calcite/Sonochan-mkII/DOC/drawings/internal_external_schema.png

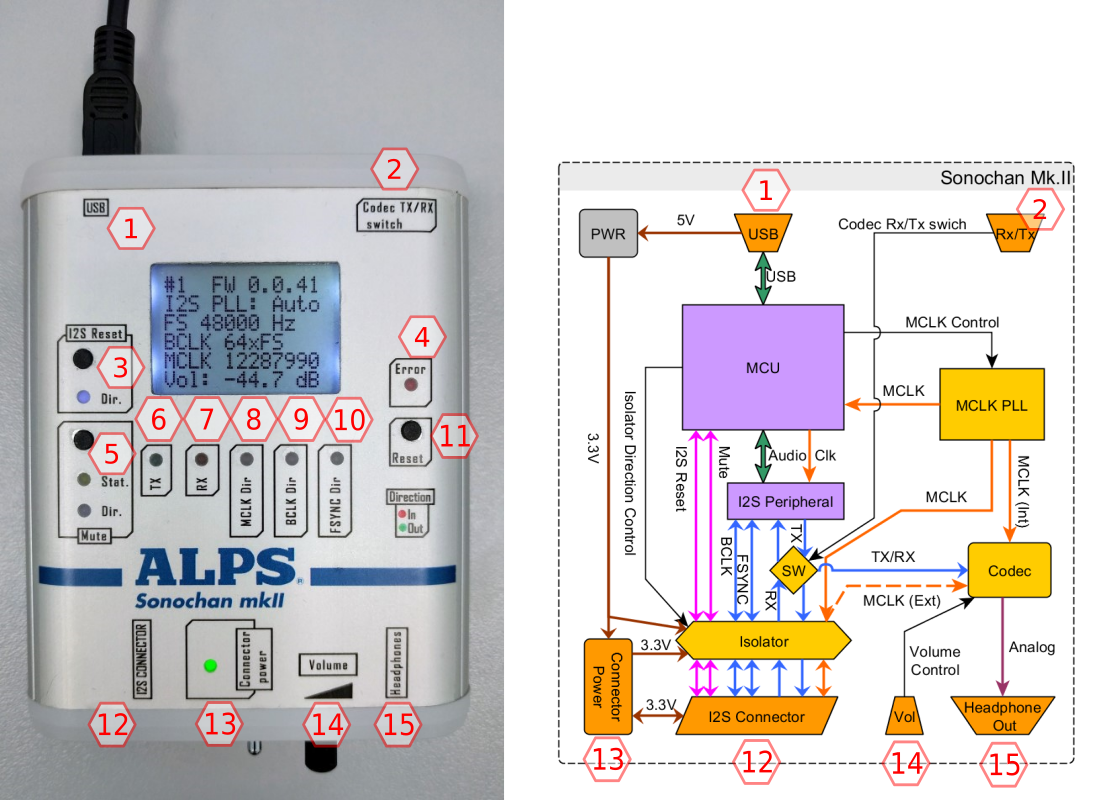
DOC/drawings/internal_external_schema.png
