calcite/Sonochan-mkII/DOC/drawings/isolation_schema.png

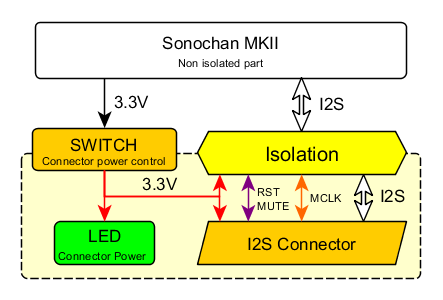
DOC/drawings/isolation_schema.png
