calcite/Sonochan-mkII/DOC/drawings/lcd_schema.png

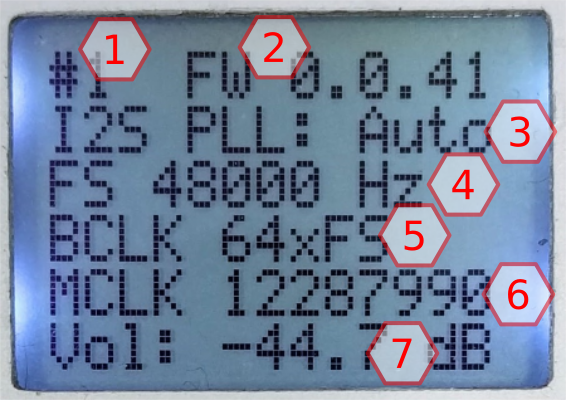
DOC/drawings/lcd_schema.png
