calcite/Sonochan-mkII/DOC/drawings/sonochan_internal_workings.png

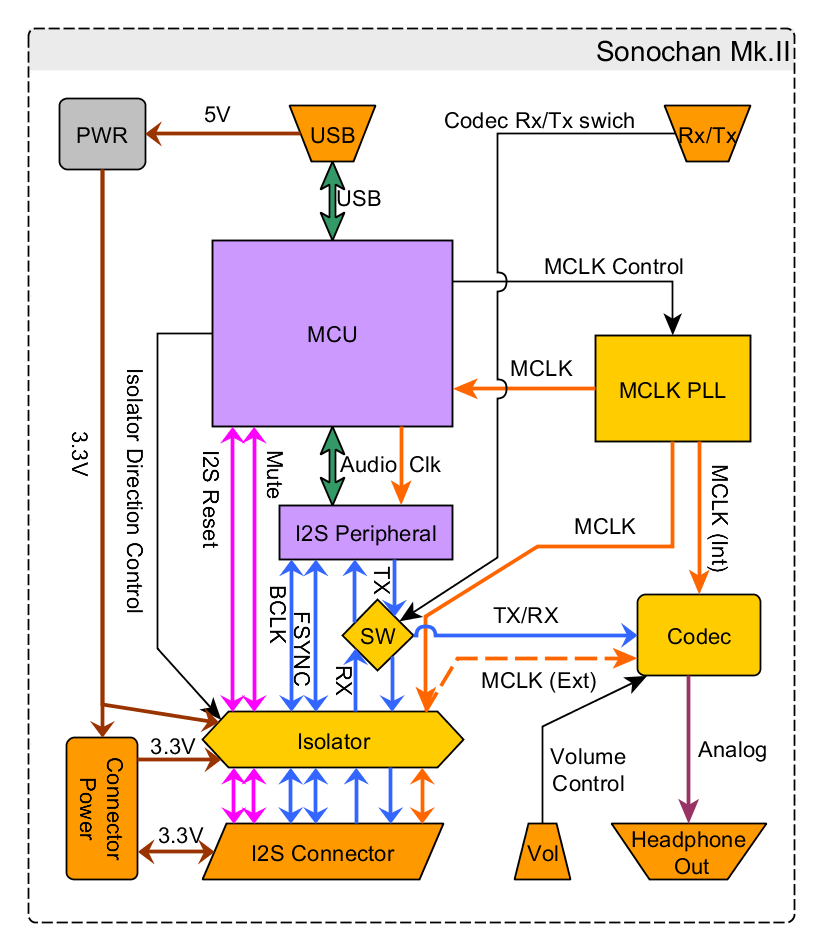
DOC/drawings/sonochan_internal_workings.png
