calcite/Sonochan-mkII/DOC/photo/snchn_mkII_complete.JPG

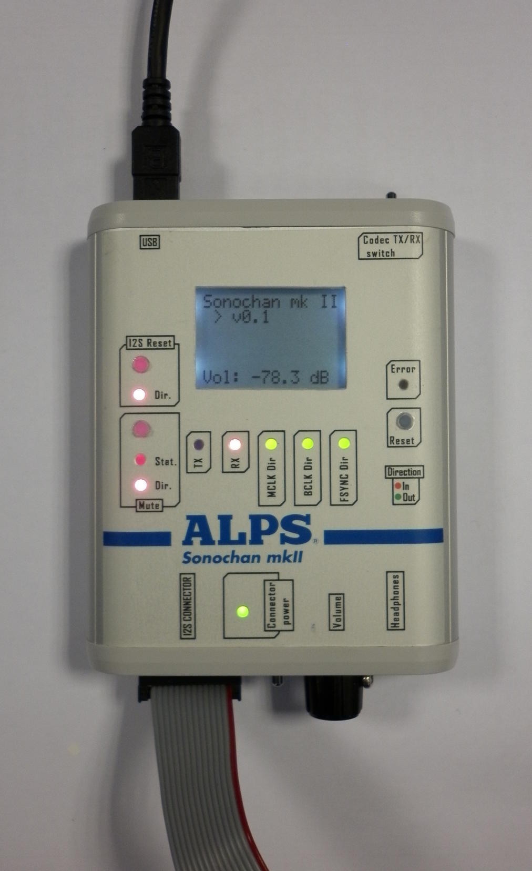
DOC/photo/snchn_mkII_complete.JPG
