calcite/Sonochan-mkII/DOC/photo/snchn_mkII_complete_enhanced.png

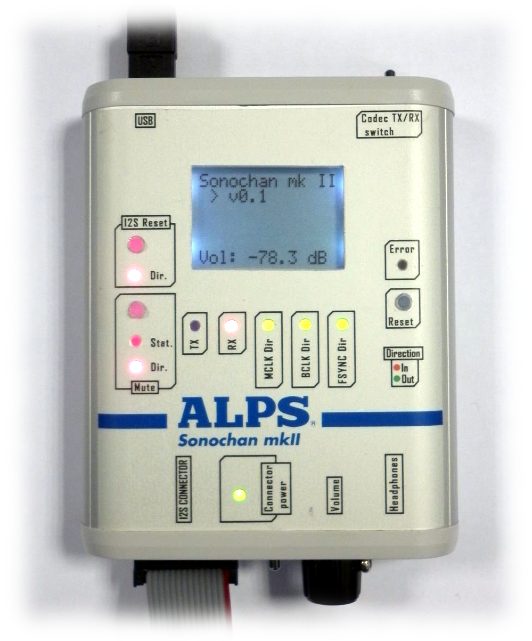
DOC/photo/snchn_mkII_complete_enhanced.png
