calcite/Sonochan-mkII/DOC/photo/snchn_mkII_complete_in_case.jpg

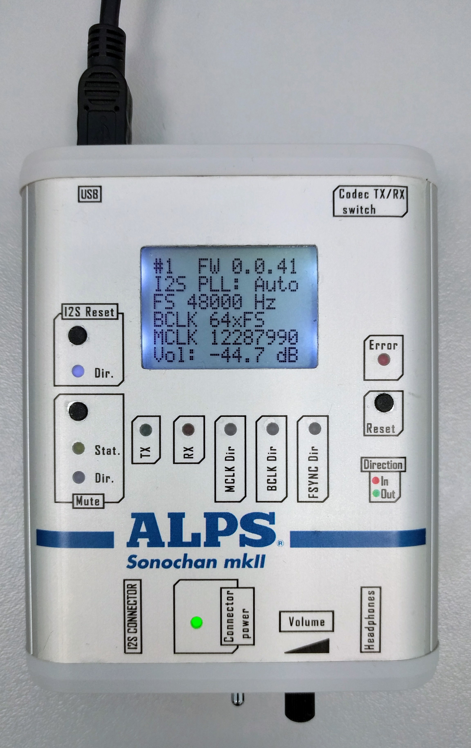
DOC/photo/snchn_mkII_complete_in_case.jpg
