calcite/Sonochan-mkII/DOC/photo/snchn_mkII_LCD_small.png

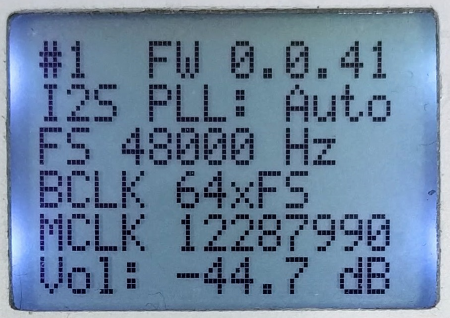
DOC/photo/snchn_mkII_LCD_small.png
