calcite/Sonochan-mkII/DOC/photo/snchn_mkII_sdr_wgt_prototype_top.JPG

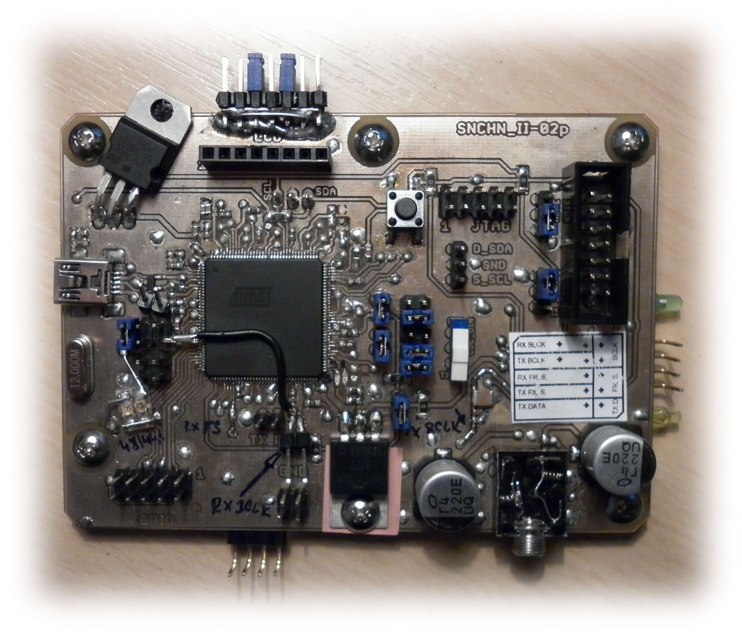
DOC/photo/snchn_mkII_sdr_wgt_prototype_top.JPG
