calcite/Sonochan-mkII/DOC/photo/snchn_mkII_top_in_case.JPG

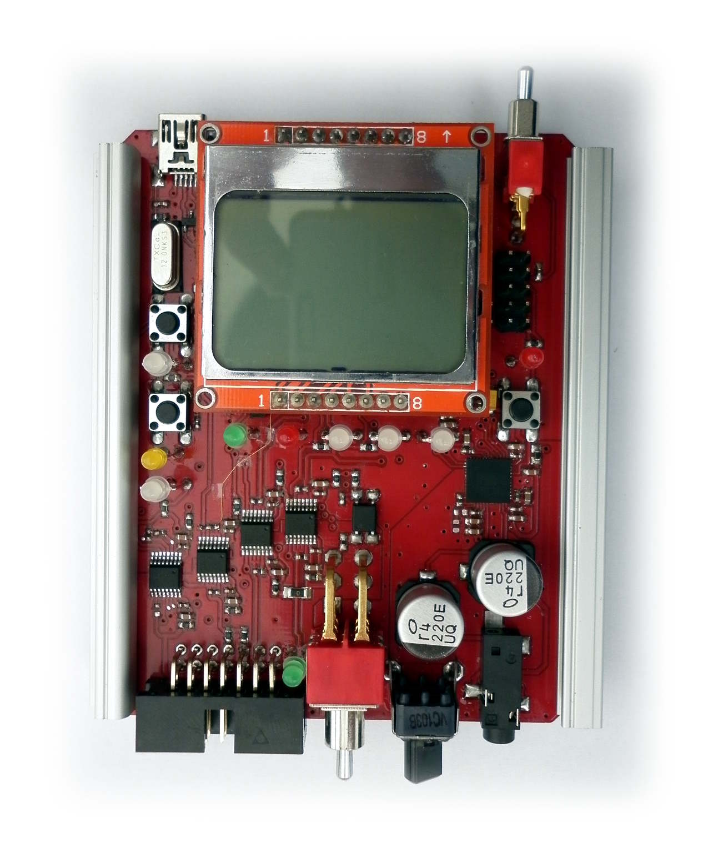
DOC/photo/snchn_mkII_top_in_case.JPG
