calcite/Sonochan-mkII/DOC/thesis/thesis_doc_files/bridge_get_metadata.gif

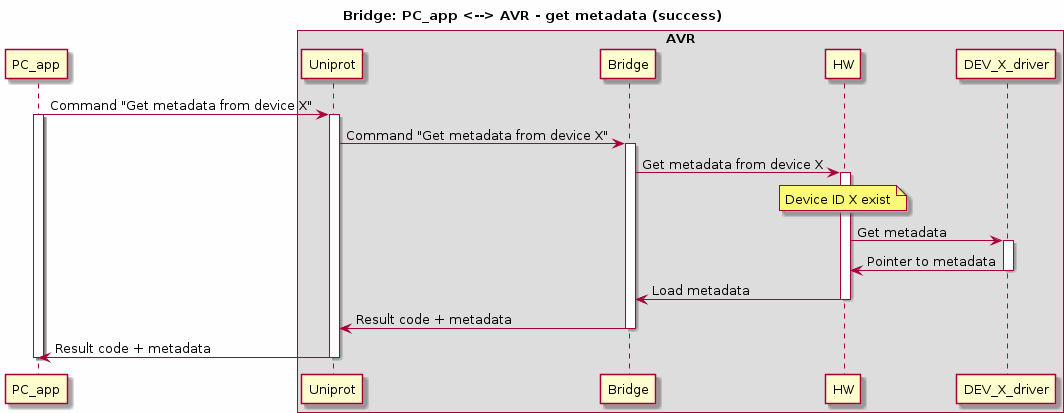
DOC/thesis/thesis_doc_files/bridge_get_metadata.gif
