calcite/Sonochan-mkII/DOC/thesis/thesis_doc_files/bridge_get_num_of_dev.gif

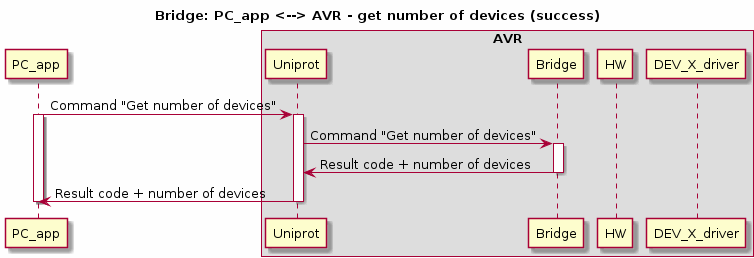
DOC/thesis/thesis_doc_files/bridge_get_num_of_dev.gif
