calcite/Sonochan-mkII/DOC/thesis/thesis_doc_files/bridge_get_setting_did_invalid.gif

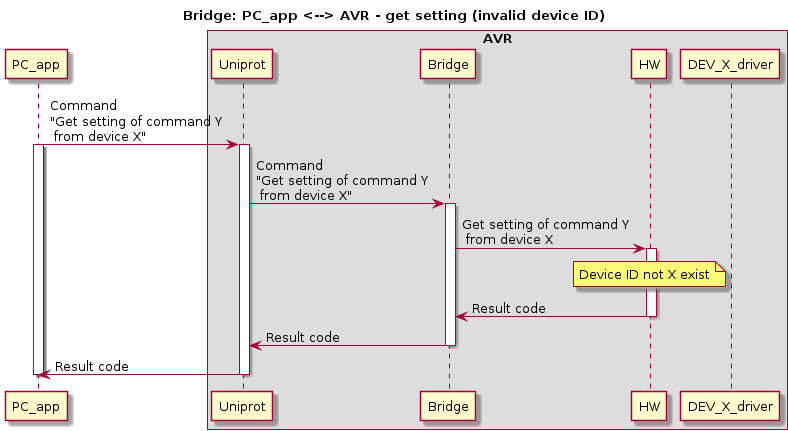
DOC/thesis/thesis_doc_files/bridge_get_setting_did_invalid.gif
