calcite/Sonochan-mkII/DOC/thesis/thesis_doc_files/bridge_set_setting_all_OK.gif

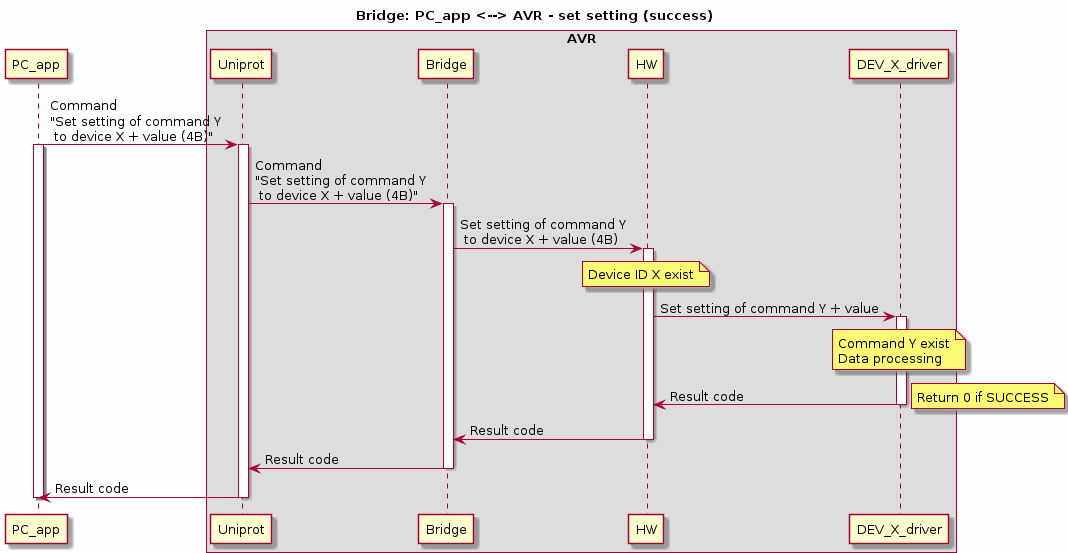
DOC/thesis/thesis_doc_files/bridge_set_setting_all_OK.gif
