calcite/Sonochan-mkII/DOC/thesis/thesis_doc_files/host_set_sampling_freq.gif

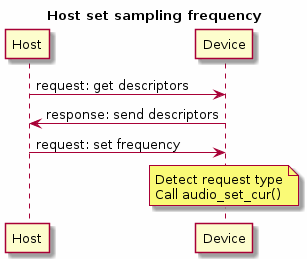
DOC/thesis/thesis_doc_files/host_set_sampling_freq.gif
