calcite/Sonochan-mkII/DOC/thesis/thesis_doc_files/uniprot_ACK.gif

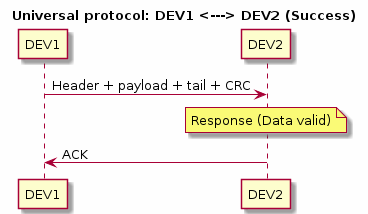
DOC/thesis/thesis_doc_files/uniprot_ACK.gif
