calcite/Sonochan-mkII/DOC/thesis/thesis_doc_files/uniprot_BUFF_OVRFLW.gif

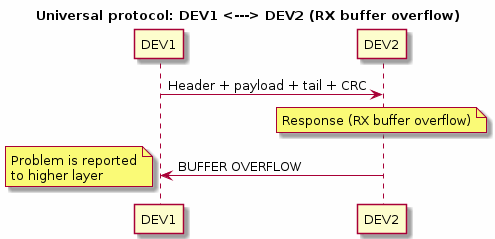
DOC/thesis/thesis_doc_files/uniprot_BUFF_OVRFLW.gif
