calcite/Sonochan-mkII/DOC/thesis/thesis_doc_files/uniprot_NACK.gif

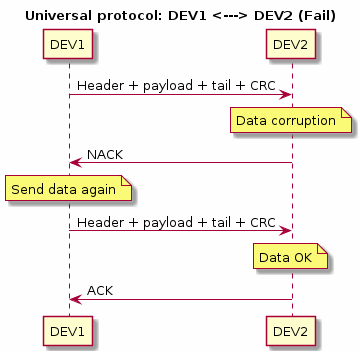
DOC/thesis/thesis_doc_files/uniprot_NACK.gif
