calcite/Sonochan-mkII/PRODUCTION_DATA/stickers/i2s_connector_description.png

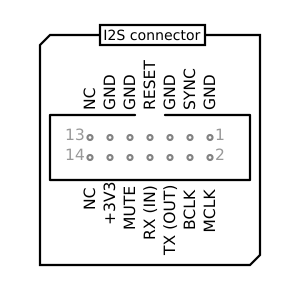
PRODUCTION_DATA/stickers/i2s_connector_description.png
