calcite/Sonochan-mkII/PRODUCTION_DATA/stickers/SNCHN_II-02p_Extra_sticker.pdf

123

11

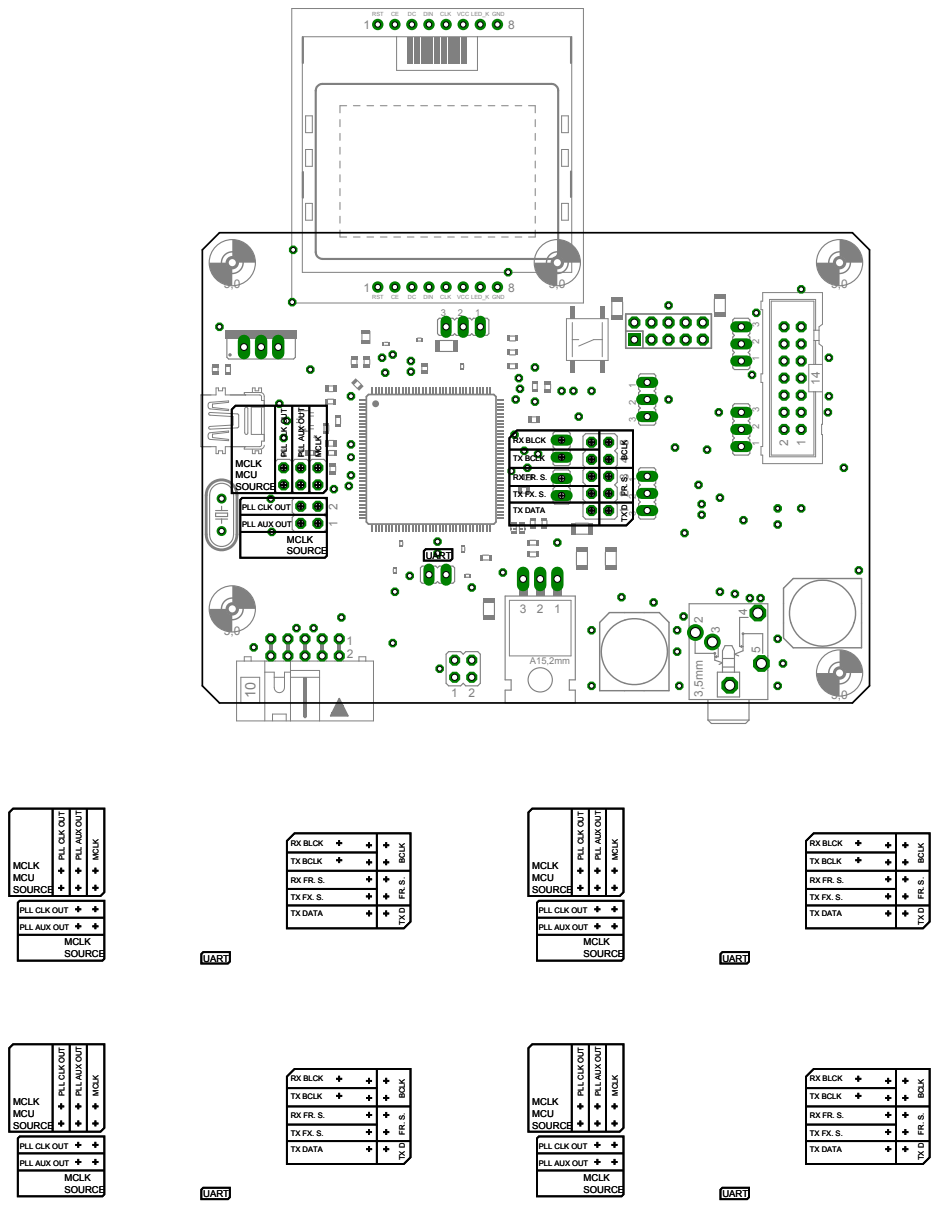
[picture p71: page 1]
RST; DC DIN CLK VCC LED_K GND; MCLK SOURCE; MCLK MCU SOURCE; MCLK; UART; BCLK; RX BLCK; TX BCLK; TX DATA

PLL CLK OUT

PLL AUX OUT
