calcite/Sonochan-mkII/HW/Eagle_exports/SNCHN_II-02p_top_mirrored.pdf

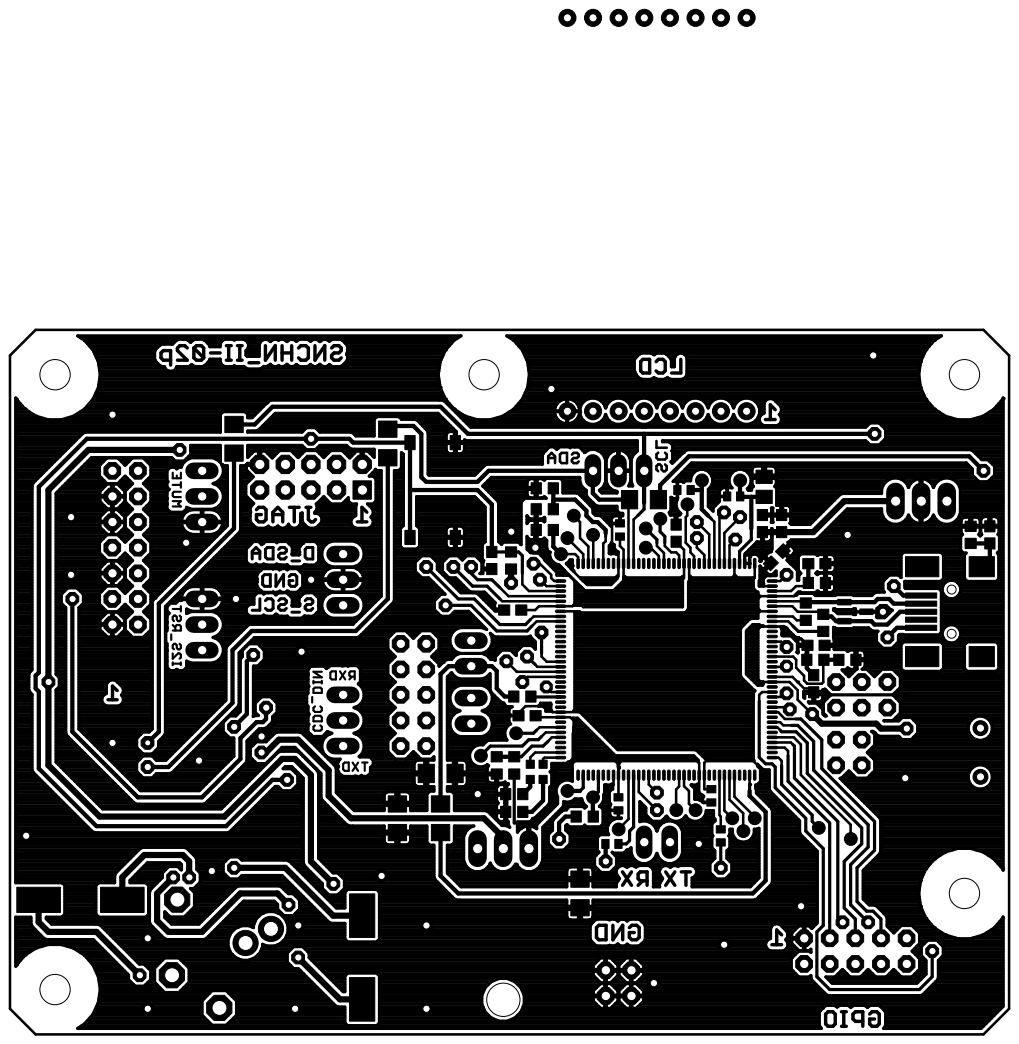
[picture p81: page 1]
