calcite/Sonochan-mkII/HW/Eagle_exports/SNCHN_II-03-brd_15.pdf

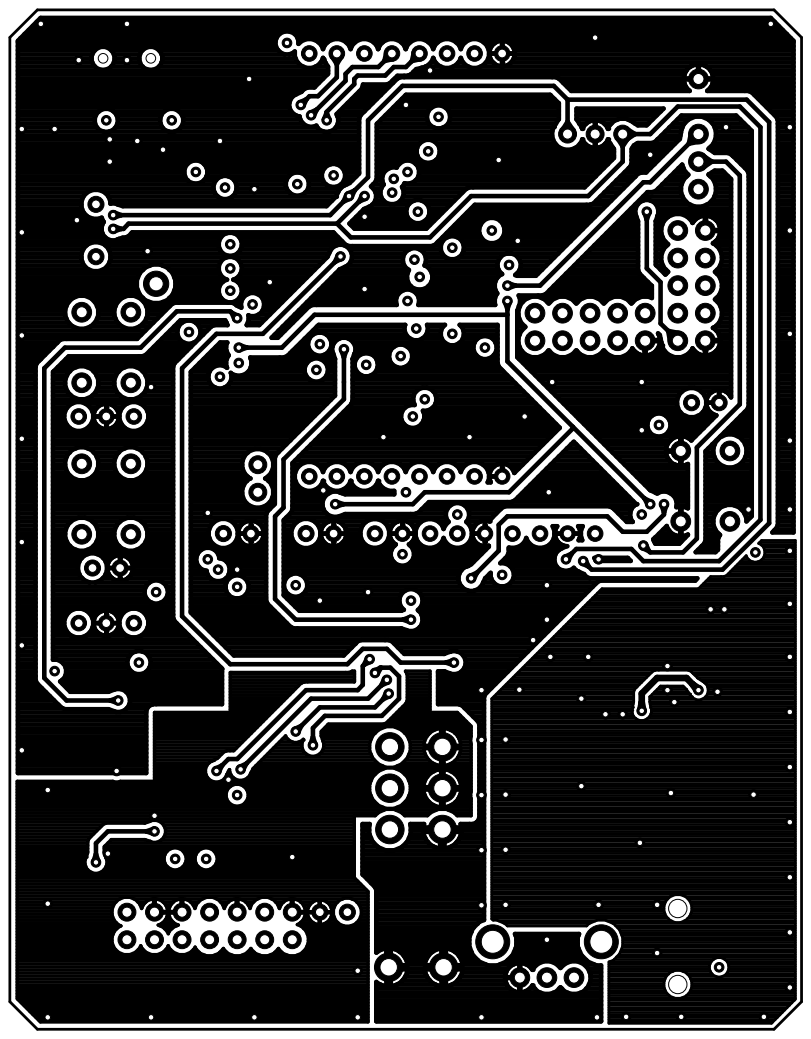
[picture p82: page 1]
