calcite/Sonochan-mkII/HW/Eagle_exports/SNCHN_II-03-brd_2.pdf

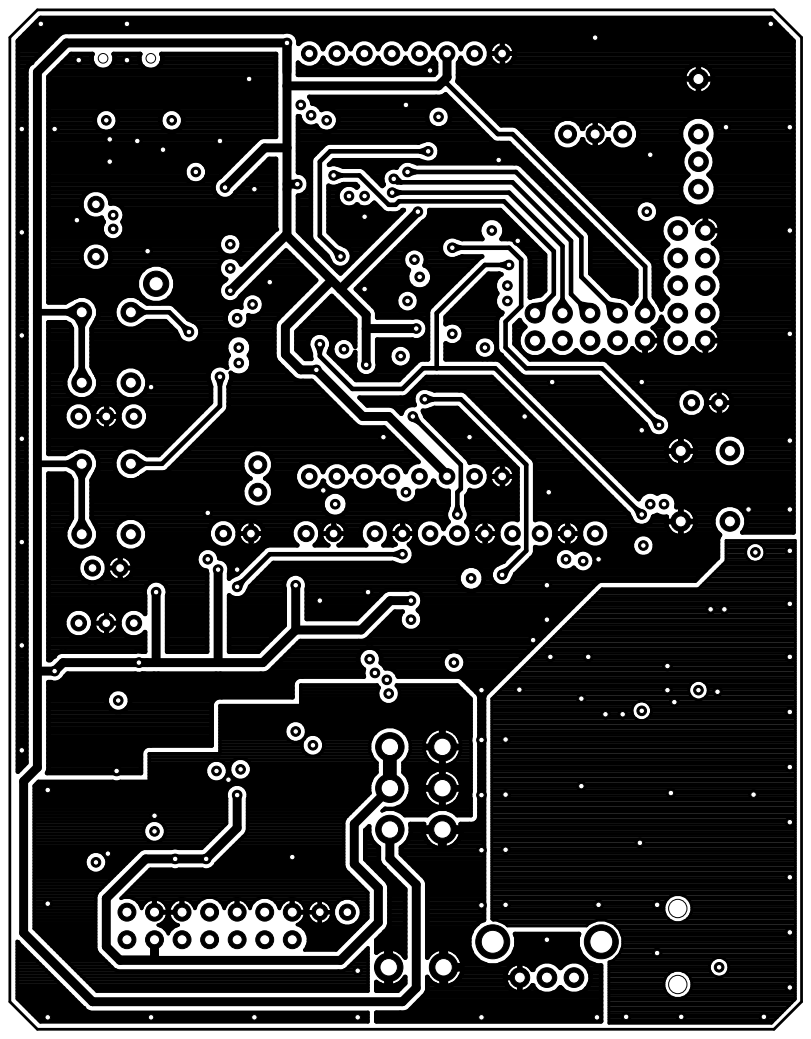
[picture p83: page 1]
