calcite/Sonochan-mkII/HW/Eagle_exports/SNCHN_II-03-brd_bottom.pdf

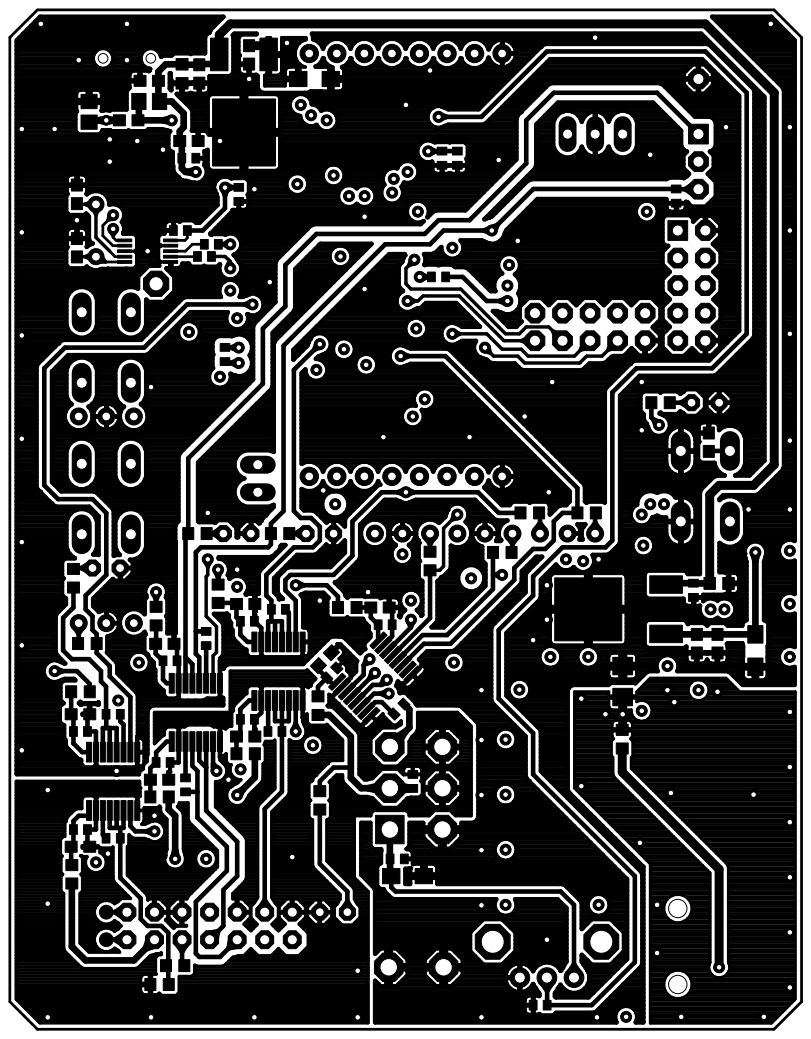
[picture p84: page 1]
