calcite/Sonochan-mkII/HW/Eagle_exports/SNCHN_II-03-brd_top.pdf

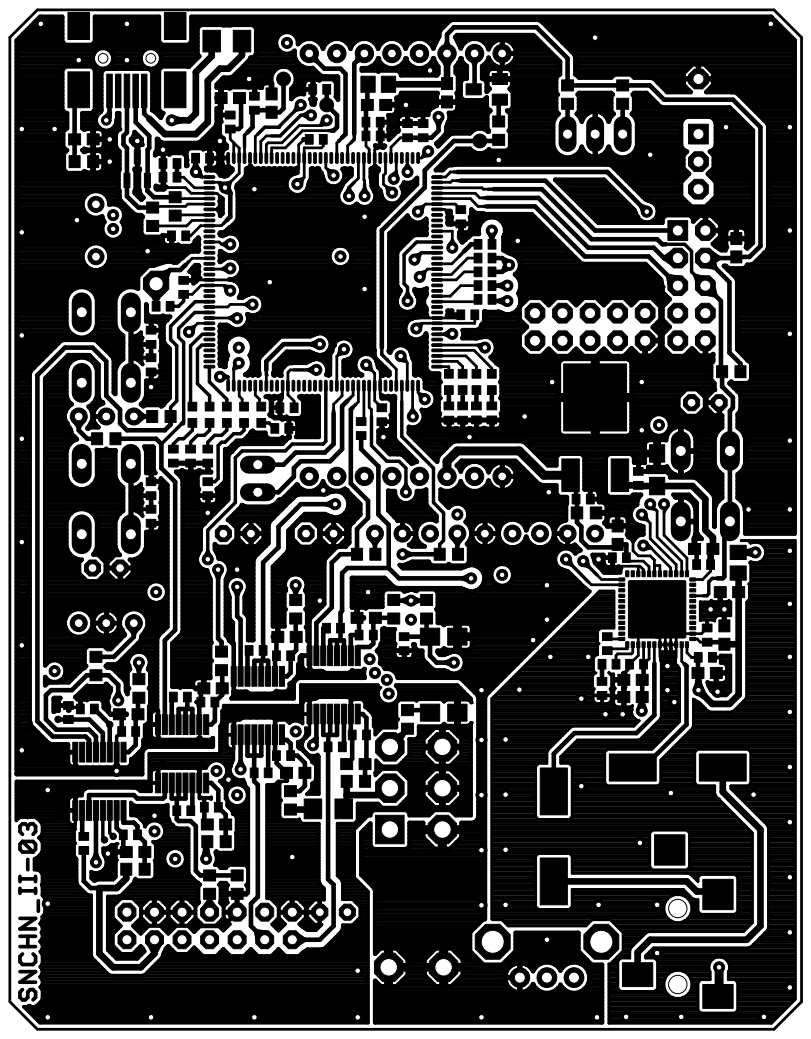
[picture p85: page 1]
