calcite/Sonochan-mkII/HW/Eagle_exports/SNCHN_II-03A-brd_15.pdf

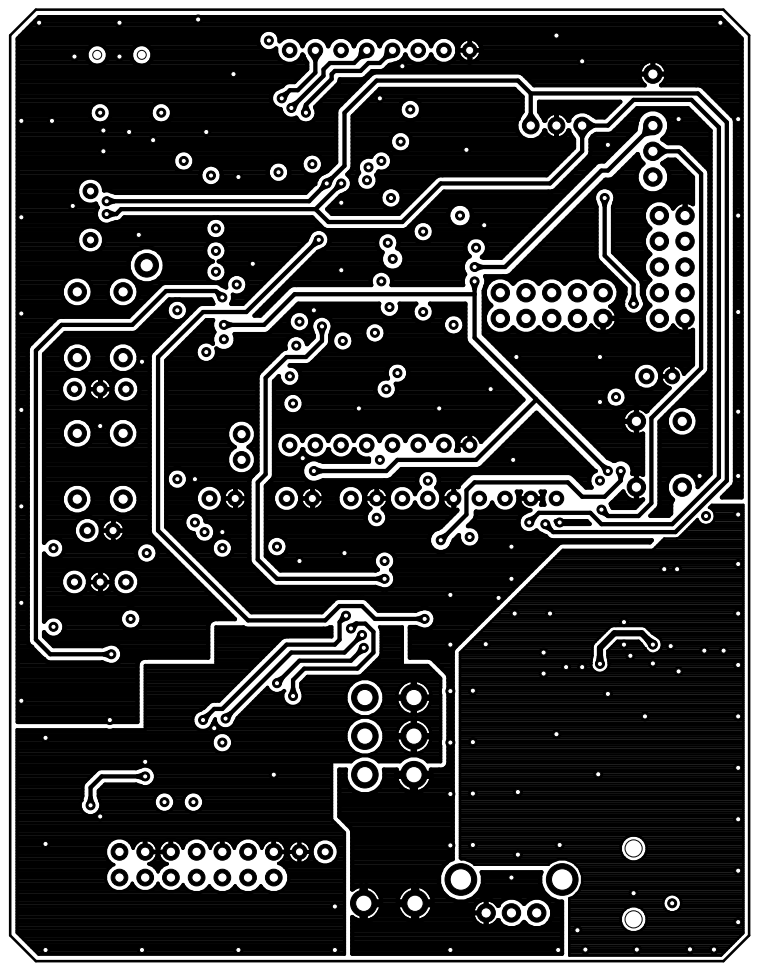
[picture p86: page 1]
