calcite/Sonochan-mkII/HW/Eagle_exports/SNCHN_II-03A-brd_16_bottom.pdf

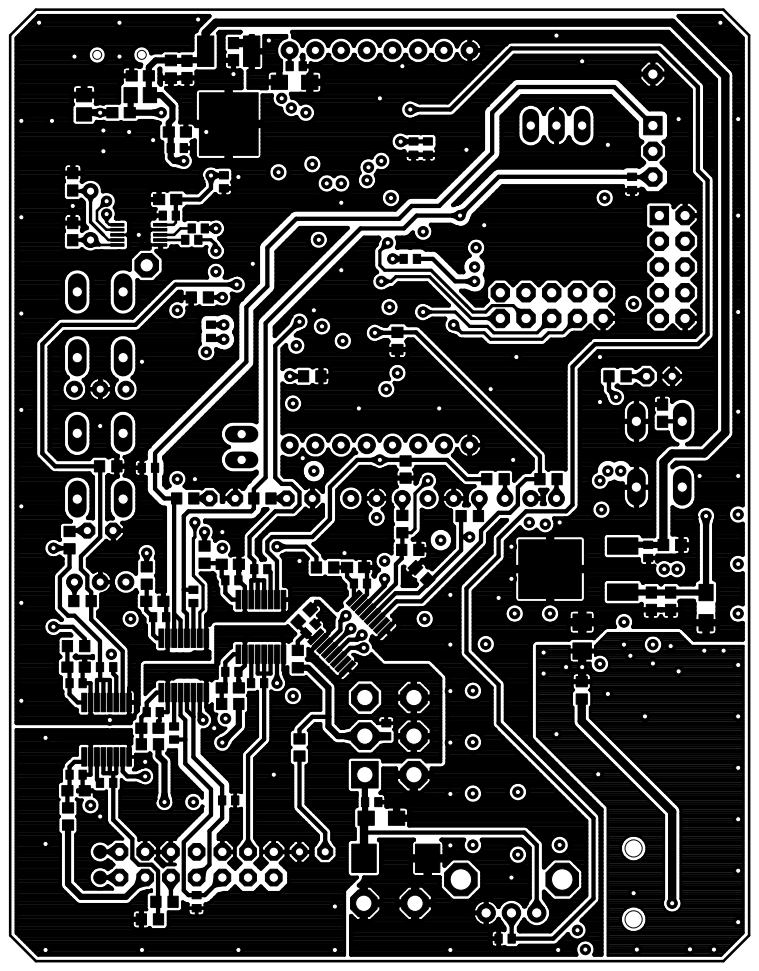
[picture p87: page 1]
