calcite/Sonochan-mkII/HW/Eagle_exports/SNCHN_II-03A-brd_1_top.pdf

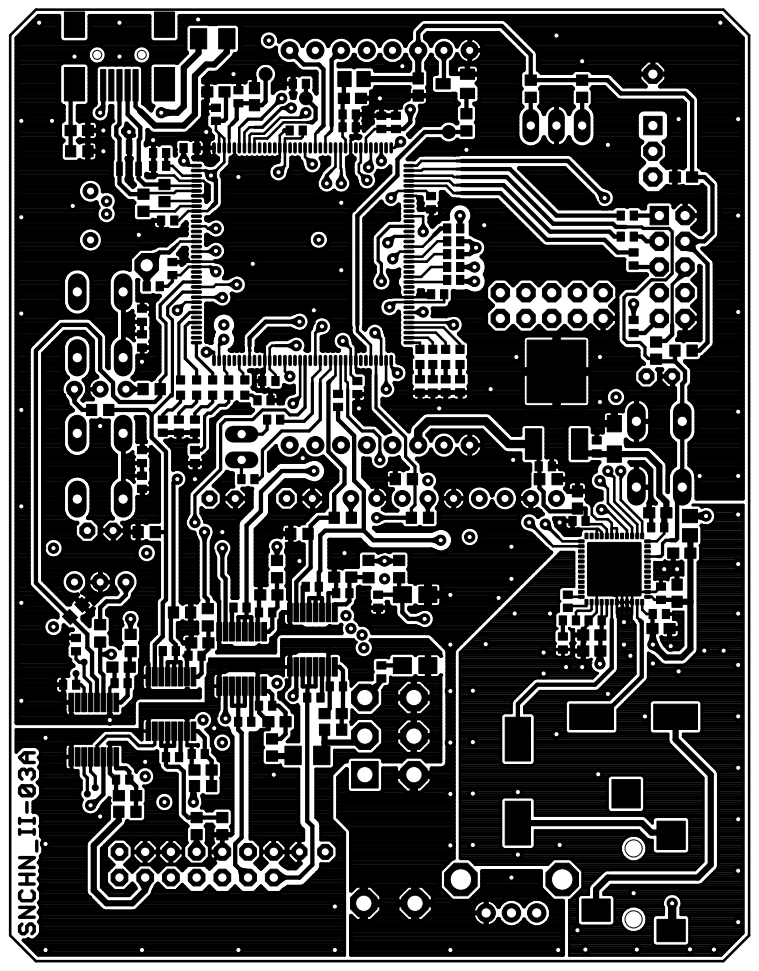
[picture p88: page 1]
