calcite/Sonochan-mkII/HW/Eagle_exports/SNCHN_II-03A-brd_2.pdf

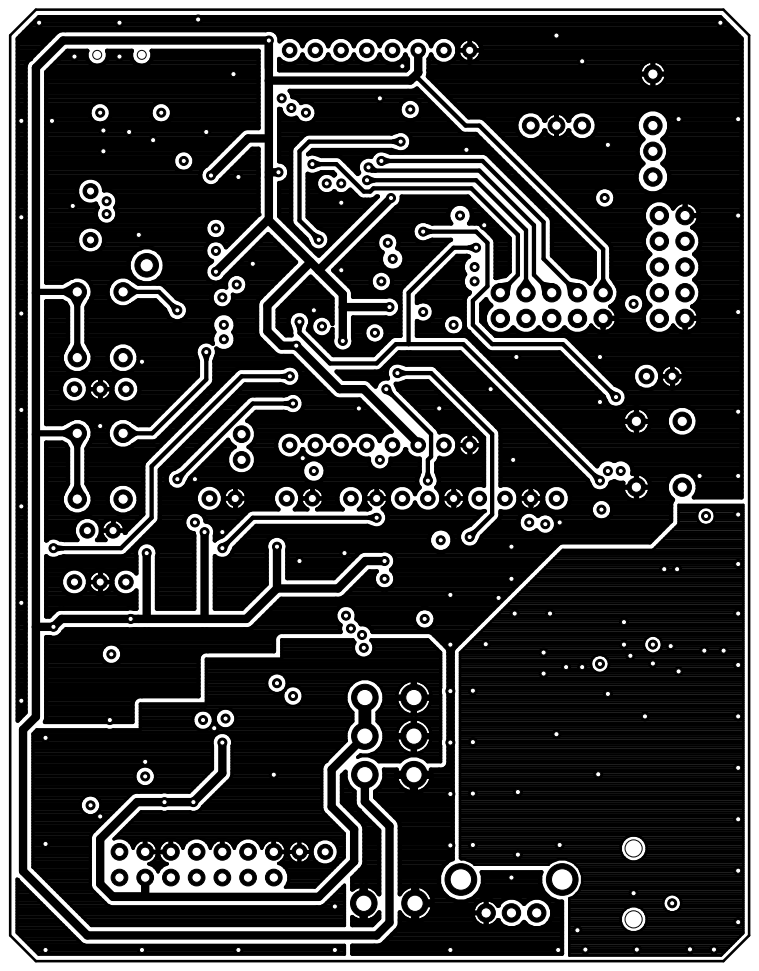
[picture p89: page 1]
