calcite/Sonochan-mkII/PRODUCTION_DATA/case/case_mx2-8-10.pdf

B-B ( 1 : 1 )
B

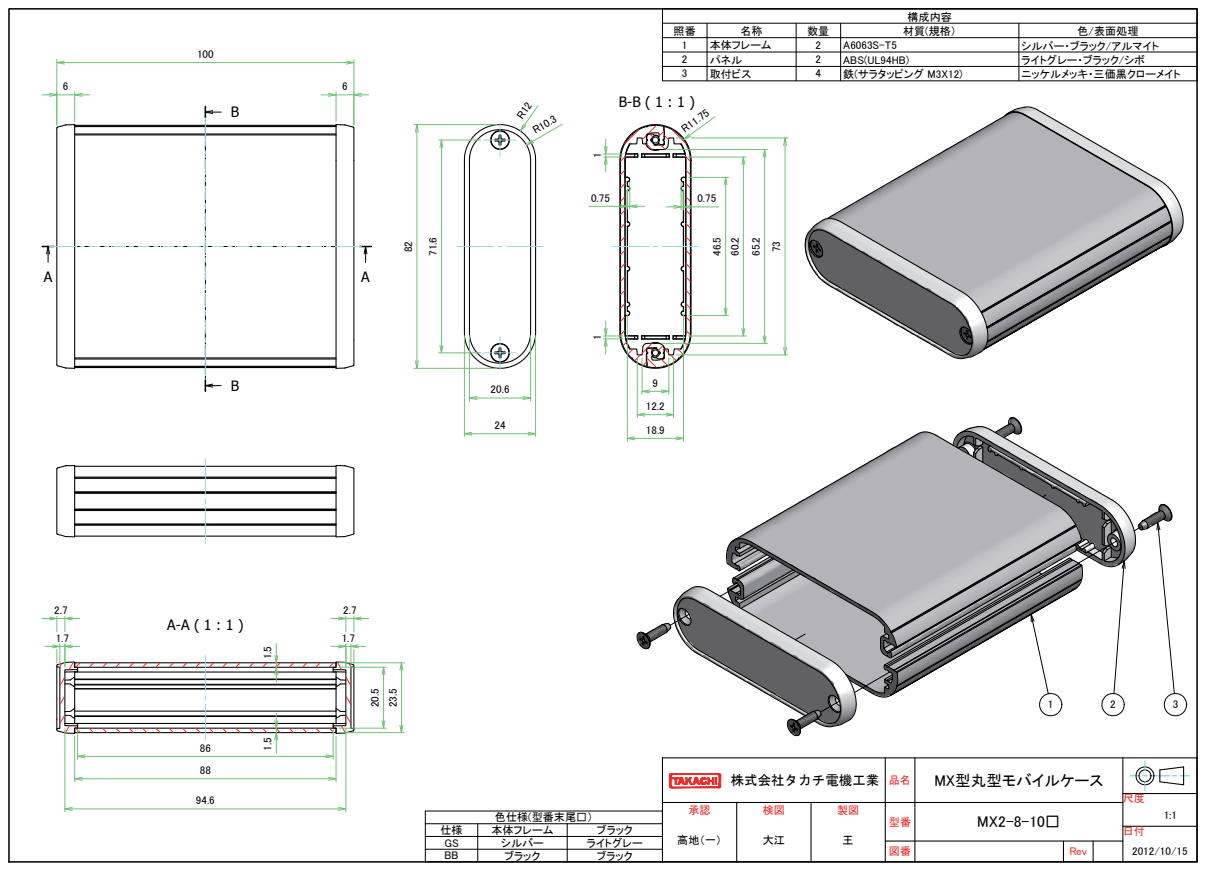
[picture p90: page 1]
株式会社タカチ電機工業; MX型丸型モバイルケース; 構成内容; 色仕様(型番末尾□）

照番 | 名称 | 数量 | 材質(規格） | 色/表面処理
1 | 本体フレーム | 2 | A6063S-T5 | シルバー・ブラック/アルマイト
2 | パネル | 2 | ABS(UL94HB) | ライトグレー・ブラック/シボ
3 | 取付ビス | 4 | 鉄(サラタッピング M3X12) | ニッケルメッキ・三価黒クローメイト

仕様 | 本体フレーム | ブラック
GS | シルバー | ライトグレー
BB | ブラック | ブラック

図番 | Rev
