calcite/Sonochan-mkII/PRODUCTION_DATA/case/Sonochan_mkII_case_dimensions.pdf

B-B ( 1 : 1 )
B

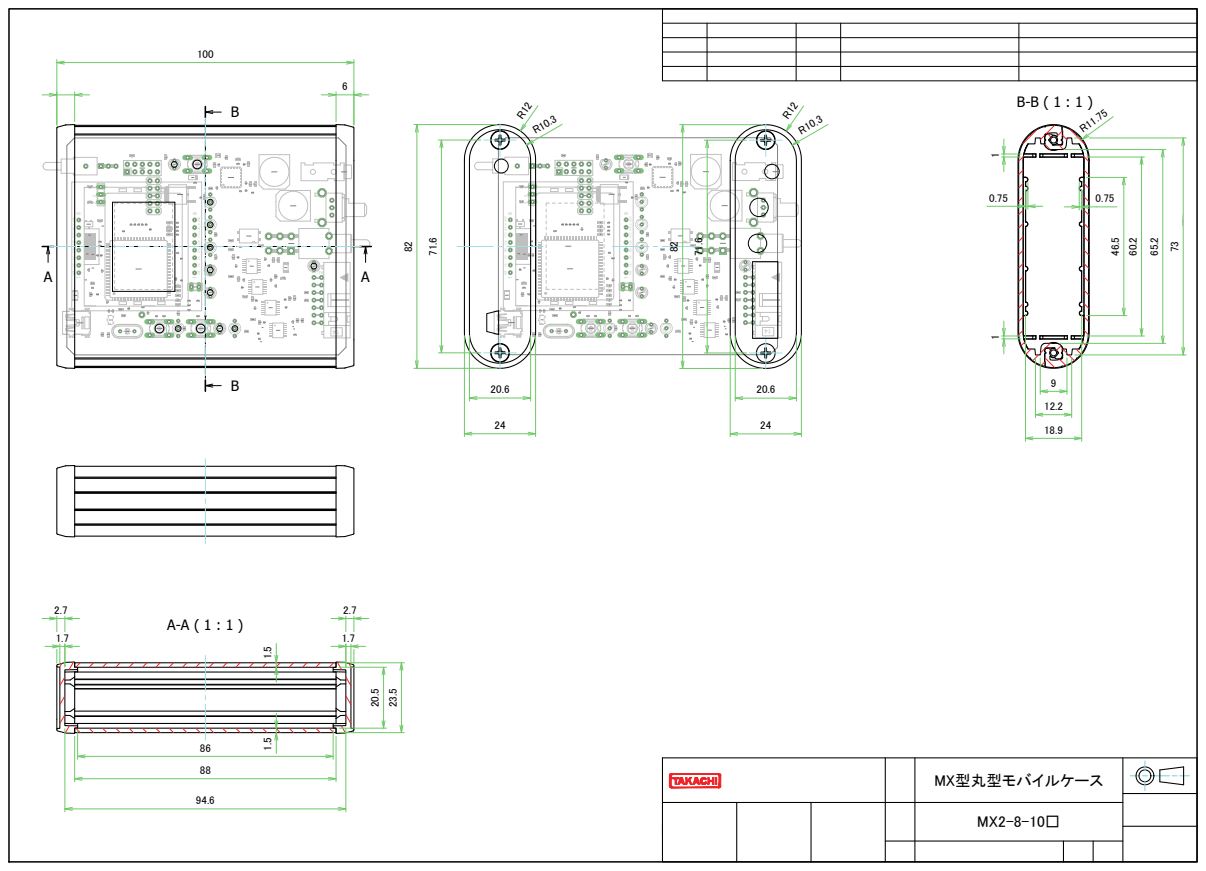
[picture p91: page 1]
MX型丸型モバイルケース
