calcite/Sonochan-mkII/FW/src/cs2200.c

/*
Sonochan Mk.II Firmware.
Copyright (C) 2013-2015 Martin Stejskal,
ALPS Electric Czech, s.r.o.,
ALPS Electric Co., Ltd.

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
Contact information:
Martin Stejskal <martin.stejskal@jp.alps.com>,
Josef Nevrly <jnevrly@alps.cz>
ALPS Electric Czech, s.r.o., Sebranice 240, 679 31 Sebranice u Boskovic
Czech Republic
*/
/**
 * \file
 *
 * \brief Driver for fractional PLL CS2200
 *
 * Created:  2014.03.12\n
 * Modified: 2015.07.15
 *
 * \version 0.7.4
 * \author Martin Stejskal
 */

#include "cs2200.h"
//============================| Global variables |=============================
/**
 * \brief Register image of CS2200.
 *
 * It is static, so it is "global" only for this file.
 *
 */
static cs2200_reg_img_t s_register_img;

/**
 * \brief Virtual register image
 *
 * This values PLL directly do not have in memory. However, there are in more\n
 * human readable format. Also some values can use generic driver (need to\n
 * point to result variables and so on).\n
 * t is static, so it is "global" only for this file.
 */
static cs2200_virtual_reg_img_t s_virtual_reg_img;



//=========================| Generic driver support |==========================
#if CS2200_SUPPORT_GENERIC_DRIVER != 0
/**
 * \brief Configure table for device
 */

// Test architecture (AVR8 versus other)
#ifdef __AVR_ARCH__
const gd_config_struct CS2200_config_table[] PROGMEM =
#else
const gd_config_struct CS2200_config_table[] =
#endif
  {
    {
      0,                      // Command ID
      "Initialize CS2200 hardware",  // Name
      "Initialize I/O and TWI module (if used)",      // Descriptor
      void_type,              // Input data type
      {.data_uint32 = 0},     // Minimum input value
      {.data_uint32 = 0},     // Maximum input value
      void_type,              // Output data type
      {.data_uint32 = 0},     // Minimum output value
      {.data_uint32 = 0},     // Maximum output value
      (GD_DATA_VALUE*)&gd_void_value, // Output value
      cs2200_init                     /* Function, that should be
                                       * called
                                       */
    },
    {
      1,
      "Set PLL frequency",
      "Frequency format: unsigned 32 bit in Hz",
      uint32_type,
      {.data_uint32 =  6000000},        // Min 6 MHz
      {.data_uint32 = 75000000},        // Max 75 MHz
      uint32_type,
      {.data_uint32 =  6000000},
      {.data_uint32 = 75000000},
      (GD_DATA_VALUE*)&s_virtual_reg_img.i_real_freq.i_32bit,
      cs2200_set_PLL_freq
    },
    {
      2,
      "Increase PLL frequency by 1",
      "Increase ratio number by 1",
      void_type,
      {.data_uint32 = 0},
      {.data_uint32 = 0},
      void_type,
      {.data_uint32 = 0},
      {.data_uint32 = 0},
      (GD_DATA_VALUE*)&gd_void_value,
      cs2200_inc_PLL_freq
    },
    {
      3,
      "Decrease PLL frequency by 1",
      "Decrease ratio number by 1",
      void_type,
      {.data_uint32 = 0},
      {.data_uint32 = 0},
      void_type,
      {.data_uint32 = 0},
      {.data_uint32 = 0},
      (GD_DATA_VALUE*)&gd_void_value,
      cs2200_dec_PLL_freq
    },
    {
      4,
      "Set ratio",
      "Unsigned 32 bit raw value",
      uint32_type,
      {.data_uint32 = 0},
      {.data_uint32 = 0xFFFFFFFF},
      uint32_type,
      {.data_uint32 = 0},
      {.data_uint32 = 0xFFFFFFFF},
      (GD_DATA_VALUE*)&s_register_img.Ratio.i_32bit,
      cs2200_set_ratio
    },
    {
      5,
      "Set output divider/multiplier ratio",
      "Input values: 1 2 4 8 0.5 0.25 0.125 0.0625",
      float_type,
      {.data_float = 0.0625},
      {.data_float = 8},
      float_type,
      {.data_float = 0.0625},
      {.data_float = 8},
      (GD_DATA_VALUE*)&s_virtual_reg_img.f_out_div_mul,
      cs2200_set_out_divider_multiplier_float
    },
    {
      6,
      "Set safe change flag (frequency change)",
      "Options: 1 - safe (recommended) ; 0 - dangerous change (may cause glitches)",
      uint8_type,
      {.data_uint8 = 0},
      {.data_uint8 = 1},
      uint8_type,
      {.data_uint8 = 0},
      {.data_uint8 = 1},
      (GD_DATA_VALUE*)&s_virtual_reg_img.i_save_change_ratio_by_1,
      cs2200_set_safe_change_ratio_by_1
    },
    {
      7,
      "Set (1) or clear (0) freeze bit",
      "Freeze bit allow configure PLL while changes are not applied",
      uint8_type,
      {.data_uint8 = 0},
      {.data_uint8 = 1},
      uint8_type,
      {.data_uint8 = 0},
      {.data_uint8 = 1},
      (GD_DATA_VALUE*)&s_virtual_reg_img.i_freeze_flag,
      cs2200_set_freeze_bit
    }
  };
/// \brief Maximum command ID (is defined by last command)
#define CS2200_MAX_CMD_ID          7


const gd_metadata CS2200_metadata =
{
        CS2200_MAX_CMD_ID,              // Max CMD ID
        "Fractional PLL CS2200-CP v0.7.3",     // Description
        (gd_config_struct*)&CS2200_config_table[0],
        0x21    // Serial number (0~255)
};
#endif


//=============================| FreeRTOS stuff |==============================
// If RTOS support is enabled, create this
#if CS2200_SUPPORT_RTOS != 0
portBASE_TYPE xStatus;
xSemaphoreHandle mutexI2C;
#endif

//==========================| High level functions |===========================
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
